zzeneg/PseudoMakeMeKeyCapProfiles/stl/Choc/Chicago_Steno_R3_home.stl

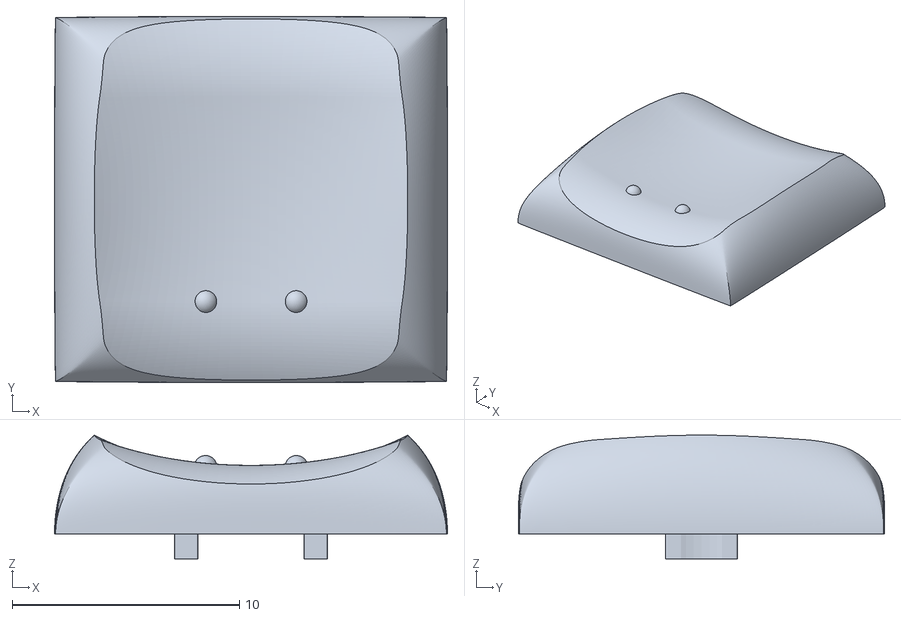
[picture p15: CAD file, 2023-03-17]
stl/Choc/Chicago_Steno_R3_home.stl
17.3 x 16.1 x 5.45
