zzeneg/PseudoMakeMeKeyCapProfiles/stl/Choc/Chicago_Steno_Convex.stl

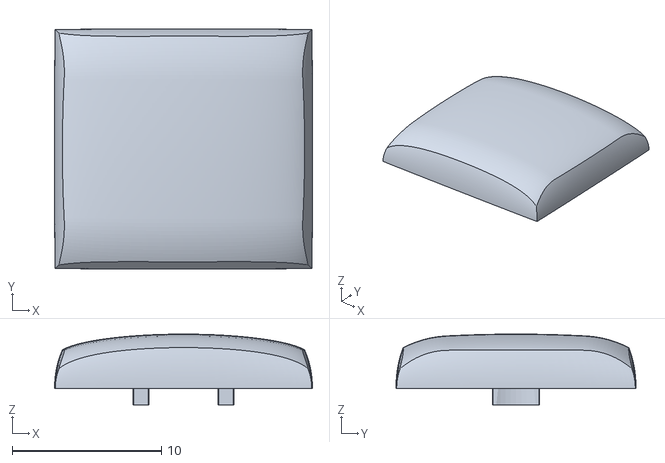
[picture p16: CAD file, 2023-03-17]
stl/Choc/Chicago_Steno_Convex.stl
17.3 x 16.1 x 4.75
