zzeneg/PseudoMakeMeKeyCapProfiles/stl/Choc/Chicago_Steno_Thumb.stl

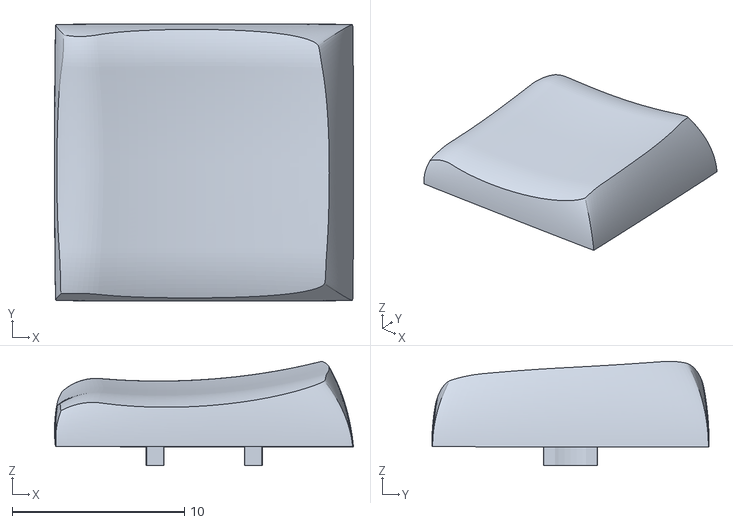
[picture p17: CAD file, 2023-03-17]
stl/Choc/Chicago_Steno_Thumb.stl
17.4 x 16.1 x 6.05
